Sinclair81/Mini-Tastatur/Images/PCB_Back.jpg

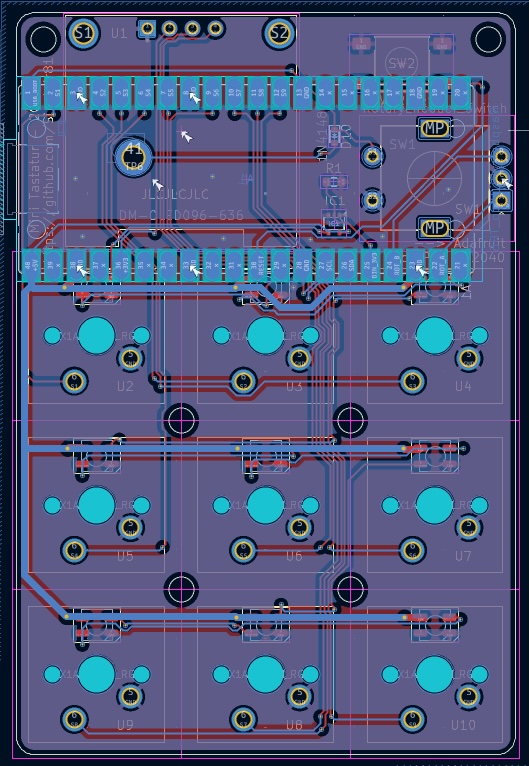
Images/PCB_Back.jpg
