Sinclair81/Mini-Tastatur/3D Print/Mini_Tastatur v14 housing bottom.jpg

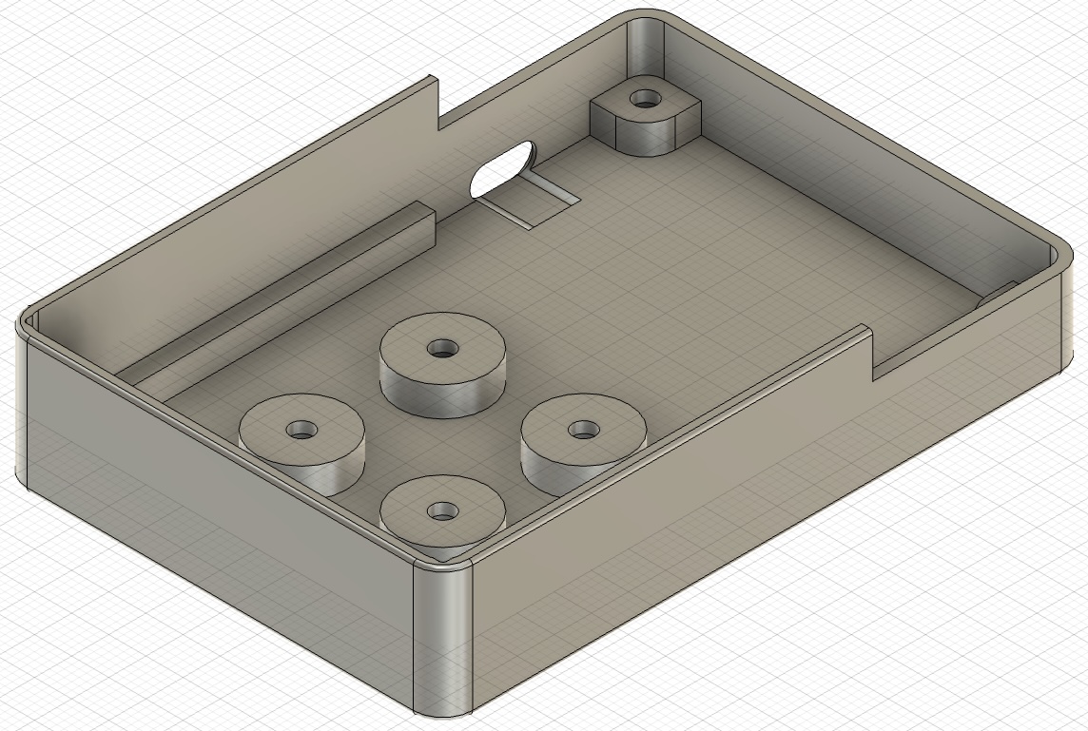
3D Print/Mini_Tastatur v14 housing bottom.jpg
